MOSH-Insa-Toulouse/2022-2023-4gp-ELLINGSEN-SZTYM/LTSpice/Circuit_initial_avec_capteur/Projet2.asc

B1: bi; I=V(cp,cn)*(10n+(v(gc,gn)*10n))
C1: cap; 1µ
R1: res; 1k
Named nets: cp, cn, gp, gn, gc
