MOSH-Insa-Toulouse/2022-2023-4gp-ELLINGSEN-SZTYM/LTSpice/Test_efficacite-filtres_&_frequence-Nyquist/Test_efficacite-filtres_&_frequence-Nyquist.asc

C1: cap; 1p
C2: cap; 100n
C6: cap; 1µ
C7: cap; 100n
R6: res; 100k
R7: res; 1k
R8: res; 100k
R9: res; 1k
R10: res; 10k
U2: LTC1050
V1: voltage; SINE(0 325 7700)
V3: voltage; 5
V4: voltage; PULSE(0 1 0.2 0.1 0.1 10); AC 1 0
X1: Projet2
Named nets: 0, ADC
;.tran 12
.ac oct 100 0.1 10000
